jpnorair/Saturn/Saturn-I/images/1600px-Saturn_symbol_.bmp

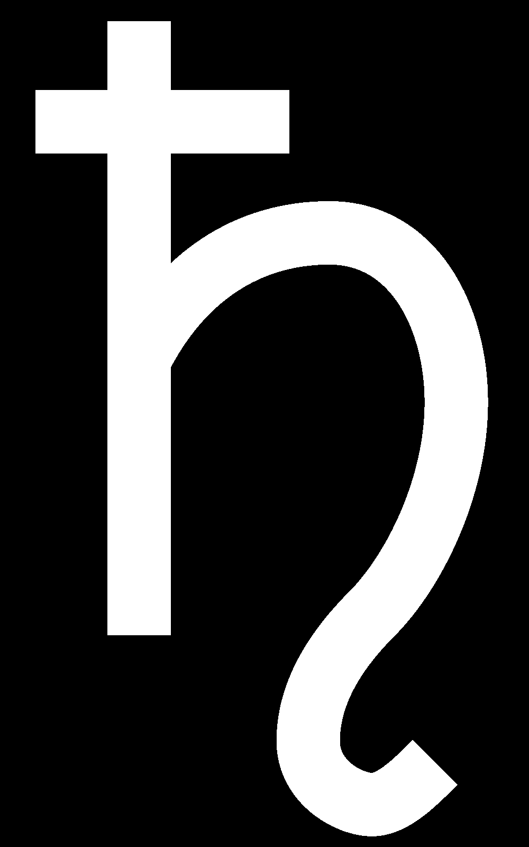
Saturn-I/images/1600px-Saturn_symbol_.bmp
